cctvfm/quadtec101/Firmware/Neuztech-1.X/waveforms.h

/* Microchip Technology Inc. and its subsidiaries.  You may use this software 
 * and any derivatives exclusively with Microchip products. 
 * 
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
 * IN NO EVENT WILL MICROCHIP BE LIABLE FOR ANY INDIRECT, SPECIAL, PUNITIVE, 
 * INCIDENTAL OR CONSEQUENTIAL LOSS, DAMAGE, COST OR EXPENSE OF ANY KIND 
 * WHATSOEVER RELATED TO THE SOFTWARE, HOWEVER CAUSED, EVEN IF MICROCHIP HAS 
 * BEEN ADVISED OF THE POSSIBILITY OR THE DAMAGES ARE FORESEEABLE.  TO THE 
 * FULLEST EXTENT ALLOWED BY LAW, MICROCHIP'S TOTAL LIABILITY ON ALL CLAIMS 
 * IN ANY WAY RELATED TO THIS SOFTWARE WILL NOT EXCEED THE AMOUNT OF FEES, IF 
 * ANY, THAT YOU HAVE PAID DIRECTLY TO MICROCHIP FOR THIS SOFTWARE.
 *
 * MICROCHIP PROVIDES THIS SOFTWARE CONDITIONALLY UPON YOUR ACCEPTANCE OF THESE 
 * TERMS. 
 */

/* 
 * File:   
 * Author: 
 * Comments:
 * Revision history: 
 */

// This is a guard condition so that contents of this file are not included
// more than once.  
#ifndef WAVEFORMS
#define	WAVEFORMS

#include <xc.h> // include processor files - each processor file is guarded.  
#define TWELVEBITMODE
//waves centered around 2048
//const unsigned int eventooth[1024]={2112,2176,2240,2304,2367,2430,2492,2554,2615,2675,2735,2793,2851,2907,2963,3017,3069,3121,3171,3220,3267,3313,3357,3399,3440,3479,3517,3553,3587,3619,3650,3678,3706,3731,3755,3776,3797,3815,3832,3847,3861,3873,3884,3893,3900,3907,3912,3915,3918,3919,3919,3919,3917,3914,3911,3906,3901,3895,3889,3882,3875,3867,3859,3851,3842,3834,3825,3816,3808,3799,3791,3783,3775,3767,3760,3753,3746,3740,3735,3730,3726,3722,3719,3716,3714,3713,3712,3712,3713,3714,3716,3719,3722,3726,3730,3735,3741,3747,3754,3762,3769,3778,3786,3795,3805,3815,3825,3835,3846,3856,3867,3878,3889,3900,3911,3922,3933,3944,3955,3965,3975,3985,3995,4004,4013,4022,4030,4038,4045,4052,4058,4064,4070,4075,4079,4083,4086,4089,4091,4093,4094,4095,4095,4095,4094,4093,4091,4089,4086,4083,4080,4076,4072,4067,4063,4058,4053,4047,4042,4036,4030,4025,4019,4013,4007,4001,3995,3989,3984,3978,3973,3967,3962,3958,3953,3949,3945,3941,3938,3934,3932,3929,3927,3925,3924,3923,3922,3921,3921,3921,3922,3923,3924,3925,3927,3929,3931,3933,3936,3939,3942,3945,3948,3951,3954,3958,3961,3964,3968,3971,3974,3977,3980,3983,3985,3987,3990,3991,3993,3994,3995,3996,3996,3996,3996,3995,3994,3992,3990,3988,3985,3982,3978,3974,3969,3964,3959,3953,3947,3940,3933,3925,3918,3910,3901,3892,3883,3874,3865,3855,3845,3835,3824,3814,3803,3793,3782,3771,3760,3749,3739,3728,3717,3707,3696,3686,3676,3666,3656,3647,3638,3628,3620,3611,3603,3595,3587,3580,3573,3566,3559,3553,3547,3542,3536,3531,3526,3522,3518,3514,3510,3506,35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

//waves centered around 0
#ifdef TWELVEBITMODE
const signed int cellowave[1024]={1,1,12,31,58,84,103,122,141,152,162,181,196,206,227,255,283,311,340,363,382,400,419,438,453,462,465,465,456,449,449,449,449,441,433,433,429,419,410,401,391,382,373,357,339,320,303,294,280,261,250,239,221,205,196,187,177,186,193,193,204,222,249,277,305,342,389,435,482,529,579,635,686,733,771,809,846,884,921,951,980,1018,1052,1080,1102,1120,1139,1155,1165,1169,1169,1169,1169,1169,1169,1169,1169,1169,1188,1207,1226,1250,1278,1306,1336,1374,1407,1435,1477,1524,1571,1621,1678,1728,1775,1821,1868,1915,1952,1980,2008,2033,2033,2033,2033,2020,2001,1982,1961,1933,1905,1876,1857,1838,1819,1800,1782,1763,1744,1725,1707,1688,1663,1635,1607,1579,1551,1518,1480,1450,1423,1404,1386,1367,1348,1329,1320,1308,1289,1270,1252,1233,1213,1184,1161,1142,1116,1088,1060,1032,1004,975,947,919,893,874,851,823,802,783,765,742,714,686,658,621,583,546,508,471,433,394,347,300,254,214,176,129,82,35,-12,-59,-105,-152,-199,-246,-293,-332,-370,-407,-441,-470,-498,-526,-545,-561,-571,-580,-589,-599,-609,-628,-647,-666,-691,-719,-747,-781,-828,-875,-922,-969,-1016,-1063,-1109,-1156,-1211,-1267,-1323,-1379,-1435,-1492,-1548,-1595,-1640,-1677,-1710,-1738,-1766,-1793,-1812,-1827,-1836,-1839,-1839,-1839,-1833,-1815,-1796,-1777,-1759,-1738,-1710,-1691,-1681,-1672,-1662,-1653,-1647,-1647,-1641,-1632,-1622,-1611,-1592,-1578,-1569,-1552,-1535,-1535,-1535,-1535,-1541,-1551,-1560,-1572,-1591,-1604,-1614,-1631,-1648,-1658,-1667,-1677,-1679,-1679,-1679,-1679,-1679,-1667,-1648,-1630,-1609,-1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
#endif

#endif	/* XC_HEADER_TEMPLATE_H */
